ReDerEE/2025_Robootika_opengloves/src/lucidgloves-main/lucidgloves-main/hardware/Prototype3.1/Prot3.1_GuideNode.STL

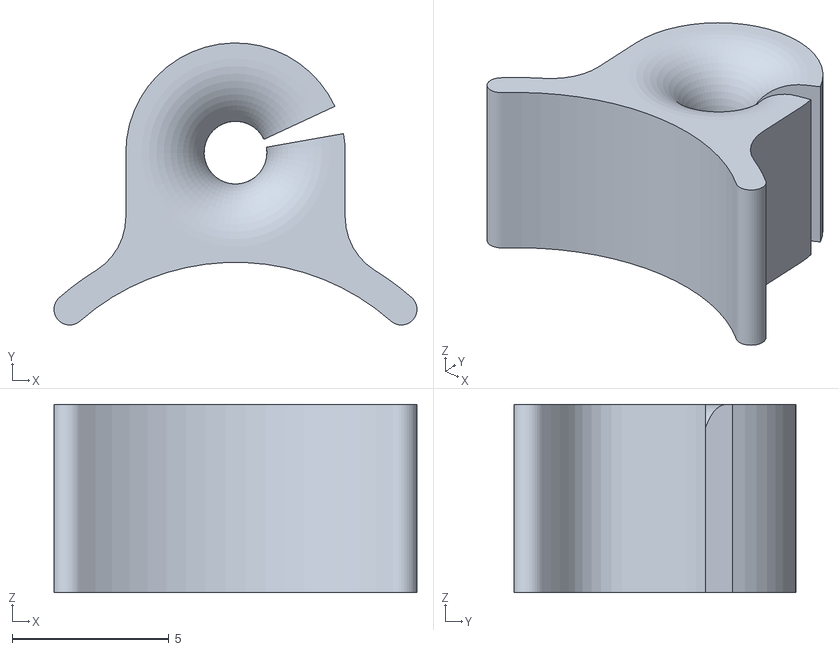
[picture p15: CAD file, 2025-12-10, an earlier design]
src/lucidgloves-main/lucidgloves-main/hardware/Prototype3.1/Prot3.1_GuideNode.STL
11.6 x 9.00 x 6.00
