ReDerEE/2025_Robootika_opengloves/src/lucidgloves-main/lucidgloves-main/hardware/Prototype3/Prot3_EndCap.STL

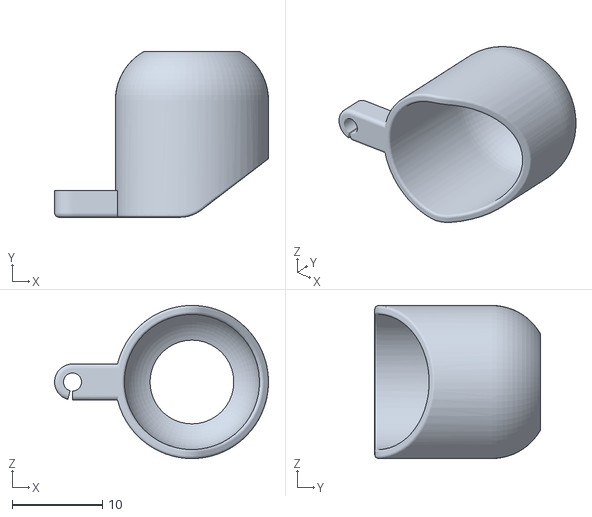
[picture p16: CAD file, 2025-12-10, an earlier design]
src/lucidgloves-main/lucidgloves-main/hardware/Prototype3/Prot3_EndCap.STL
23.8 x 18.4 x 17.0
